BubbaTLC/author-clock/main/display_mgr.c

#include "display_mgr.h"

#include <stdio.h>
#include <string.h>
#include <stdlib.h>
#include "esp_log.h"
#include "esp_netif.h"
#include "nvs_config.h"

#include "EPD_7in5_V2.h"
#include "GUI_Paint.h"
#include "bmfont_renderer.h"
#include "fonts/font_select.h"
#include "weather_icons.h"

static const char *TAG = "DISPLAY_MGR";

// ─── Layout constants ────────────────────────────────────────────────────────
#define EPD_W 800
#define EPD_H 480

#define TIME_X 10
// Top bar height: must clear two font_ui lines (23+2+23=48px) plus padding → 70px
#define HRULE_Y 70
// Time text: one font_ui line (23px) vertically centred in [0, HRULE_Y]
#define TIME_Y ((HRULE_Y - 23) / 2) // = 23

// Weather block: right-aligned in the top bar, computed dynamically at render time
// Centre the 2-line text block (48px) in [0, HRULE_Y]; icon starts at same top edge
#define WEATHER_ICON_Y ((HRULE_Y - 48) / 2) // = 11
#define WEATHER_TEXT_GAP 6                  // pixels between icon right edge and text
#define WEATHER_MAX_X (EPD_W - 8)           // right boundary
#define WEATHER_MIN_LEFT 300                // keep clear of date/time on the left

// Quote area
#define QUOTE_X 20
#define QUOTE_MAX_WIDTH 760
#define ATTRIB_MAX_WIDTH (EPD_W - QUOTE_X - 8)

// ─── Image buffer ─────────────────────────────────────────────────────────────
#define IMAGE_SIZE (EPD_W * EPD_H / 8)
static uint8_t *s_image = NULL;
static bool s_initialized = false;

// ─── Helper: enhanced word-wrap with bmfont support ──────────────────────────
// Returns the Y position immediately after the last drawn line (useful for placing
// elements dynamically below the text block). Handles timeString portion in bold.
// ─── Helper: measure line width using the correct font per segment ─────────────
// Uses bold_font for characters that fall within [ts_pos, ts_pos+ts_len),
// regular font for everything else. Matches how the line will actually be drawn.
static uint16_t mixed_string_width(const char *p, int len, const bmfont_t *font,
                                   const bmfont_t *bold_font, const char *ts_pos, int ts_len) {
    char buf[512];
    int n;

    // Fast path: no bold overlap in this segment
    if (!bold_font || !ts_pos || ts_len == 0 || ts_pos >= p + len || ts_pos + ts_len <= p) {
        n = len < (int)sizeof(buf) - 1 ? len : (int)sizeof(buf) - 1;
        memcpy(buf, p, n);
        buf[n] = '\0';
        return bmfont_string_width(buf, font);
    }

    uint16_t w = 0;

    // Prefix in regular font: [p, ts_pos)
    if (ts_pos > p) {
        n = (int)(ts_pos - p);
        n = n < (int)sizeof(buf) - 1 ? n : (int)sizeof(buf) - 1;
        memcpy(buf, p, n);
        buf[n] = '\0';
        w += bmfont_string_width(buf, font);
    }

    // Bold section: intersect [ts_pos, ts_pos+ts_len) with [p, p+len)
    const char *bold_start = ts_pos > p ? ts_pos : p;
    const char *bold_end = (ts_pos + ts_len) < (p + len) ? (ts_pos + ts_len) : (p + len);
    if (bold_end > bold_start) {
        n = (int)(bold_end - bold_start);
        n = n < (int)sizeof(buf) - 1 ? n : (int)sizeof(buf) - 1;
        memcpy(buf, bold_start, n);
        buf[n] = '\0';
        w += bmfont_string_width(buf, bold_font);
    }

    // Suffix in regular font: [ts_pos+ts_len, p+len)
    if (ts_pos + ts_len < p + len) {
        const char *sfx = ts_pos + ts_len;
        n = (int)((p + len) - sfx);
        n = n < (int)sizeof(buf) - 1 ? n : (int)sizeof(buf) - 1;
        memcpy(buf, sfx, n);
        buf[n] = '\0';
        w += bmfont_string_width(buf, font);
    }

    return w;
}

static int text_wrap_bmfont(const char *text, const char *timestring, const bmfont_t *font,
                            const bmfont_t *bold_font, uint16_t x, uint16_t y, uint16_t max_width,
                            uint16_t max_y, bool dry_run) {
    if (!text || !font)
        return 0;

    uint16_t line_height = bmfont_height(font);
    uint16_t bold_line_height = bold_font ? bmfont_height(bold_font) : line_height;
    if (bold_line_height > line_height)
        line_height = bold_line_height;

    int lines = 0;
    uint16_t cur_y = y;

    char line_buf[128];
    const char *p = text;
    const char *timestring_pos = timestring ? strstr(text, timestring) : NULL;
    int ts_len = (timestring && timestring_pos) ? (int)strlen(timestring) : 0;

    while (*p && cur_y + line_height <= max_y) {
        // Find how many characters fit on this line (word-boundary break)
        int len = 0;
        int last_space = -1;
        uint16_t line_width = 0;

        // Calculate how much text fits, measuring bold sections with bold_font
        while (p[len]) {
            if (p[len] == ' ') {
                // Don't use spaces inside the timestring as break points — the
                // timestring must stay on a single line so it renders fully bold.
                bool in_ts = timestring_pos && ts_len > 0 && (p + len) >= timestring_pos &&
                             (p + len) < (timestring_pos + ts_len);
                if (!in_ts)
                    last_space = len;
            }
            if (p[len] == '\n') {
                last_space = len;
                break;
            }

            line_width = mixed_string_width(p, len + 1, font, bold_font, timestring_pos, ts_len);

            if (line_width >= max_width) {
                break;
            }

            len++;
        }

        // If the remaining text fits entirely, take it all
        if (p[len] == '\0') {
            // fall through with len as-is
        } else if (last_space > 0) {
            len = last_space; // break at last word boundary
        } else if (len == 0) {
            len = 1; // Force at least one character to avoid infinite loop
        }

        // Copy line
        int copy = len < (int)sizeof(line_buf) - 1 ? len : (int)sizeof(line_buf) - 1;
        memcpy(line_buf, p, copy);
        line_buf[copy] = '\0';

        if (!dry_run) {
            // Check if this line contains the timestring
            bool has_timestring =
                timestring_pos && (timestring_pos >= p) && (timestring_pos < p + len);

            if (has_timestring && bold_font && timestring) {
                int prefix_len = timestring_pos - p;
                int timestring_len = strlen(timestring);

                uint16_t cur_x = x;

                if (prefix_len > 0) {
                    char prefix[128];
                    int prefix_copy = prefix_len < 127 ? prefix_len : 127;
                    memcpy(prefix, p, prefix_copy);
                    prefix[prefix_copy] = '\0';
                    cur_x += bmfont_draw_string(cur_x, cur_y, prefix, font, BLACK, WHITE);
                }

                cur_x += bmfont_draw_string(cur_x, cur_y, timestring, bold_font, BLACK, WHITE);

                const char *suffix = timestring_pos + timestring_len;
                if (suffix < p + len) {
                    int suffix_len = (p + len) - suffix;
                    if (suffix_len > 0 && suffix_len < 128) {
                        char suffix_buf[128];
                        memcpy(suffix_buf, suffix, suffix_len);
                        suffix_buf[suffix_len] = '\0';
                        bmfont_draw_string(cur_x, cur_y, suffix_buf, font, BLACK, WHITE);
                    }
                }
            } else {
                bmfont_draw_string(x, cur_y, line_buf, font, BLACK, WHITE);
            }
        }

        // Advance past the line content and optional space/newline
        p += len;
        if (*p == ' ' || *p == '\n')
            p++;

        cur_y += line_height;
        lines++;
    }
    return cur_y;
}

// ─── Helper: clean text encoding issues ───────────────────────────────────────
static void clean_text_encoding(char *text) {
    if (!text)
        return;

    char *p = text;
    while (*p) {
        // Replace UTF-8 smart quotes with regular ASCII quotes
        if ((unsigned char)*p == 0xe2 && (unsigned char)*(p + 1) == 0x80) {
            if ((unsigned char)*(p + 2) == 0x98 || (unsigned char)*(p + 2) == 0x99) {
                // Left/right single quotes → regular apostrophe
                *p = '\'';
                memmove(p + 1, p + 3, strlen(p + 3) + 1);
            } else if ((unsigned char)*(p + 2) == 0x9c || (unsigned char)*(p + 2) == 0x9d) {
                // Left/right double quotes → regular quotes
                *p = '"';
                memmove(p + 1, p + 3, strlen(p + 3) + 1);
            } else if ((unsigned char)*(p + 2) == 0x94) {
                // Em dash → regular dash
                *p = '-';
                memmove(p + 1, p + 3, strlen(p + 3) + 1);
            } else {
                p++;
            }
        } else if ((unsigned char)*p >= 128) {
            // Replace any other non-ASCII characters with space
            *p = ' ';
            p++;
        } else {
            p++;
        }
    }
}

// ─── Helper: format combined date/time string ────────────────────────────────
static void format_datetime_string(char *buf, size_t len, uint8_t hour, uint8_t min,
                                   const char *date_str, bool use_24_hour) {
    if (!buf || !date_str)
        return;

    if (use_24_hour) {
        snprintf(buf, len, "%s, %02d:%02d", date_str, hour, min);
    } else {
        // Convert to 12-hour format
        const char *period = "AM";
        uint8_t display_hour = hour;

        if (hour == 0) {
            display_hour = 12; // midnight
        } else if (hour == 12) {
            period = "PM"; // noon
        } else if (hour > 12) {
            display_hour = hour - 12;
            period = "PM";
        }

        snprintf(buf, len, "%s, %d:%02d %s", date_str, display_hour, min, period);
    }
}

// ─── Helper: commit buffer to display ────────────────────────────────────────
// Always re-init before displaying: the display enters deep sleep after each
// EPD_7IN5_V2_Sleep() call and must be woken with a full init sequence before
// it will respond to commands or toggle the BUSY pin again.
static void flush_display(void) {
    EPD_7IN5_V2_Init();
    EPD_7IN5_V2_Display(s_image);
    EPD_7IN5_V2_Sleep();
}

// ─── Public API ──────────────────────────────────────────────────────────────

int display_mgr_init(void) {
    if (s_initialized)
        return 0;

    ESP_LOGI(TAG, "Initializing e-paper display");

    if (DEV_Module_Init() != 0) {
        ESP_LOGE(TAG, "DEV_Module_Init failed");
        return -1;
    }

    // Give the display hardware time to stabilize after power-on
    vTaskDelay(pdMS_TO_TICKS(2000));

    s_image = malloc(IMAGE_SIZE);
    if (!s_image) {
        ESP_LOGE(TAG, "Failed to allocate image buffer (%d bytes)", IMAGE_SIZE);
        return -2;
    }

    Paint_NewImage(s_image, EPD_W, EPD_H, ROTATE_0, WHITE);
    Paint_Clear(WHITE);

    // First initialization after cold boot - may need retry
    ESP_LOGI(TAG, "Performing initial EPD setup (may take extra time on cold boot)");
    for (int attempt = 0; attempt < 2; attempt++) {
        if (attempt > 0) {
            ESP_LOGW(TAG, "Retrying EPD initialization (attempt %d)", attempt + 1);
            vTaskDelay(pdMS_TO_TICKS(3000)); // Extra delay between attempts
        }

        EPD_7IN5_V2_Init();
        // Don't do initial clear on cold boot - it often fails and isn't necessary
        // since we'll be updating with content immediately anyway
        break;
    }

    s_initialized = true;
    ESP_LOGI(TAG, "Display initialized (800x480, %d byte buffer)", IMAGE_SIZE);
    return 0;
}

void display_mgr_show_provisioning(const char *ap_ssid, const char *ip_str) {
    if (!s_initialized)
        return;
    ESP_LOGI(TAG, "Showing provisioning screen");

    Paint_Clear(WHITE);

    bmfont_draw_string(10, 80, "Author Clock Setup", &font_ui, BLACK, WHITE);
    bmfont_draw_string(10, 130, "1. Connect your phone to WiFi:", &font_ui, BLACK, WHITE);

    char ssid_line[64];
    snprintf(ssid_line, sizeof(ssid_line), "   \"%s\"", ap_ssid ? ap_ssid : "AuthorClock");
    bmfont_draw_string(10, 155, ssid_line, &font_ui, BLACK, WHITE);

    bmfont_draw_string(10, 210, "2. Open a browser and visit:", &font_ui, BLACK, WHITE);

    char url_line[64];
    snprintf(url_line, sizeof(url_line), "   http://%s", ip_str ? ip_str : "192.168.4.69");
    bmfont_draw_string(10, 235, url_line, &font_ui, BLACK, WHITE);

    bmfont_draw_string(10, 295, "3. Fill in the form with your", &font_ui, BLACK, WHITE);
    bmfont_draw_string(10, 318, "   WiFi credentials and city.", &font_ui, BLACK, WHITE);

    flush_display();
}

void display_mgr_show_connecting(const char *ssid) {
    if (!s_initialized)
        return;
    ESP_LOGI(TAG, "Showing connecting screen for: %s", ssid ? ssid : "?");

    Paint_Clear(WHITE);
    bmfont_draw_string(10, 200, "Connecting to WiFi...", &font_ui, BLACK, WHITE);

    if (ssid) {
        char buf[64];
        snprintf(buf, sizeof(buf), "\"%s\"", ssid);
        bmfont_draw_string(10, 240, buf, &font_ui, BLACK, WHITE);
    }

    flush_display();
}

void display_mgr_show_error(const char *msg) {
    if (!s_initialized)
        return;
    ESP_LOGE(TAG, "Showing error: %s", msg ? msg : "(null)");

    Paint_Clear(WHITE);
    bmfont_draw_string(10, 190, "Error:", &font_ui, BLACK, WHITE);

    if (msg) {
        text_wrap_bmfont(msg, NULL, &font_ui, NULL, 10, 230, EPD_W - 20, EPD_H - 20, false);
    }

    flush_display();
}

void display_mgr_update(uint8_t time_h, uint8_t time_m, const char *date_str,
                        const quote_result_t *quote, const weather_data_t *weather) {
    if (!s_initialized)
        return;
    ESP_LOGI(TAG, "Updating display: %02d:%02d", time_h, time_m);

    Paint_Clear(WHITE);

    // ── Load display preferences ──────────────────────────────────────────────
    bool use_24_hour = true;
    date_display_mode_t date_mode = DATE_MODE_DATE_TIME;
    bool weather_enabled = true;
    temp_unit_t temp_unit = TEMP_UNIT_FAHRENHEIT;

    nvs_config_load_time_format(&use_24_hour);
    nvs_config_load_date_mode(&date_mode);
    nvs_config_load_weather_enabled(&weather_enabled);
    nvs_config_load_temp_unit(&temp_unit);

    // Suppress weather block if data isn't available yet
    bool show_weather = weather_enabled && weather && weather->valid;
    bool top_bar_visible = (date_mode != DATE_MODE_OFF) || show_weather;

    // ── Top bar ───────────────────────────────────────────────────────────────
    if (top_bar_visible) {
        // Date / time in top-left
        if (date_mode == DATE_MODE_DATE_ONLY) {
            bmfont_draw_string(TIME_X, TIME_Y, date_str ? date_str : "--", &font_ui, BLACK, WHITE);
        } else if (date_mode == DATE_MODE_DATE_TIME) {
            char datetime_str[80];
            format_datetime_string(datetime_str, sizeof(datetime_str), time_h, time_m, date_str,
                                   use_24_hour);
            bmfont_draw_string(TIME_X, TIME_Y, datetime_str, &font_ui, BLACK, WHITE);
        }

        // Weather in top-right
        if (show_weather) {
            // Build text strings first so we can measure them
            char temp_str[16];
            if (temp_unit == TEMP_UNIT_FAHRENHEIT) {
                int temp_f = (int)((weather->temp_c * 9.0f / 5.0f) + 32.0f + 0.5f);
                snprintf(temp_str, sizeof(temp_str),
                         "%d\xb0"
                         "F",
                         temp_f);
            } else {
                int temp_c = (int)(weather->temp_c + 0.5f);
                snprintf(temp_str, sizeof(temp_str),
                         "%d\xb0"
                         "C",
                         temp_c);
            }

            // Measure text widths to compute right-aligned block position
            uint16_t temp_w = bmfont_string_width(temp_str, &font_ui);
            uint16_t cond_w = bmfont_string_width(weather->condition, &font_ui);
            uint16_t text_block_w = temp_w > cond_w ? temp_w : cond_w;
            uint16_t total_w = ICON_SIZE + WEATHER_TEXT_GAP + text_block_w;
            uint16_t icon_x = (total_w < (WEATHER_MAX_X - WEATHER_MIN_LEFT))
                                  ? (WEATHER_MAX_X - total_w)
                                  : WEATHER_MIN_LEFT;
            uint16_t text_x = icon_x + ICON_SIZE + WEATHER_TEXT_GAP;

            // Draw icon
            weather_icon_draw(icon_x, WEATHER_ICON_Y, weather->icon, weather->weather_id);

            // Draw temp on first line of weather block
            bmfont_draw_string(text_x, WEATHER_ICON_Y, temp_str, &font_ui, BLACK, WHITE);

            // Draw condition on second line
            uint16_t text_line2_y = WEATHER_ICON_Y + bmfont_height(&font_ui) + 2;
            if (text_line2_y < HRULE_Y - 2) {
                bmfont_draw_string(text_x, text_line2_y, weather->condition, &font_ui, BLACK,
                                   WHITE);
            }
        }

        // Horizontal rule
        Paint_DrawLine(0, HRULE_Y, EPD_W, HRULE_Y, BLACK, DOT_PIXEL_1X1, LINE_STYLE_SOLID);
    }

    // ── Vertical centering for quote ──────────────────────────────────────────
    uint16_t quote_area_top = top_bar_visible ? (HRULE_Y + 10) : 0;
    uint16_t attrib_h = bmfont_height(&font_attrib);
    uint16_t body_h = bmfont_height(&font_body);

    // Determine early whether attribution fits on one line or needs two
    bool has_quote = (quote && quote->quote[0]);
    int attrib_lines = 1;
    char attrib_full[288];
    if (has_quote) {
        snprintf(attrib_full, sizeof(attrib_full), "%s - %s", quote->title, quote->author);
        if (bmfont_string_width(attrib_full, &font_attrib) > ATTRIB_MAX_WIDTH)
            attrib_lines = 2;
    }

    // Reserve bottom margin for attribution (lines × height + 30px gap + 10px padding)
    uint16_t attrib_total = (uint16_t)(attrib_lines * attrib_h) + 40;
    uint16_t available_h = EPD_H - quote_area_top - attrib_total;

    // Build the text for measurement
    char quoted_text[1026];
    char no_quote_msg[96];
    char time_str[16];
    const char *display_text = NULL;
    const char *display_ts = NULL;

    if (has_quote) {
        snprintf(quoted_text, sizeof(quoted_text), "\"%s\"", quote->quote);
        clean_text_encoding(quoted_text);
        display_text = quoted_text;
        display_ts = (quote->timestring[0]) ? quote->timestring : NULL;
    } else {
        if (use_24_hour) {
            snprintf(time_str, sizeof(time_str), "%02d:%02d", time_h, time_m);
        } else {
            uint8_t display_hour = time_h;
            const char *ampm = "AM";
            if (time_h == 0) {
                display_hour = 12;
            } else if (time_h == 12) {
                ampm = "PM";
            } else if (time_h > 12) {
                display_hour = time_h - 12;
                ampm = "PM";
            }
            snprintf(time_str, sizeof(time_str), "%d:%02d %s", display_hour, time_m, ampm);
        }
        snprintf(no_quote_msg, sizeof(no_quote_msg),
                 "Oh no looks like this time doesn't have a quote, but it is %s.", time_str);
        display_text = no_quote_msg;
        display_ts = time_str;
    }

    // Dry-run to measure quote block height
    // Use a large max_y so the full text is measured regardless of display limits
    int measured_end_y = text_wrap_bmfont(display_text, display_ts, &font_body, &font_body_bold,
                                          QUOTE_X, 0, QUOTE_MAX_WIDTH, EPD_H, true);
    uint16_t quote_block_h = (uint16_t)(measured_end_y > 0 ? measured_end_y : body_h);

    // Center the quote block in the available area (clamp to avoid overlap with top bar)
    uint16_t quote_y = quote_area_top;
    if (available_h > quote_block_h) {
        quote_y = quote_area_top + (available_h - quote_block_h) / 2;
    }

    // ── Quote ─────────────────────────────────────────────────────────────────
    uint16_t quote_max_y = EPD_H - attrib_total;
    int quote_end_y = text_wrap_bmfont(display_text, display_ts, &font_body, &font_body_bold,
                                       QUOTE_X, quote_y, QUOTE_MAX_WIDTH, quote_max_y, false);

    // ── Attribution ───────────────────────────────────────────────────────────
    if (has_quote) {
        int attrib_y = quote_end_y + 30;
        if (attrib_lines == 2) {
            // Two-line attribution: "{title} -" / "{author}"
            if (attrib_y > (int)(EPD_H - 2 * attrib_h - 4))
                attrib_y = EPD_H - 2 * attrib_h - 4;
            char title_line[288];
            snprintf(title_line, sizeof(title_line), "%s -", quote->title);
            bmfont_draw_string(QUOTE_X, (uint16_t)attrib_y, title_line, &font_attrib, BLACK, WHITE);
            bmfont_draw_string(QUOTE_X, (uint16_t)(attrib_y + attrib_h), quote->author,
                               &font_attrib, BLACK, WHITE);
        } else {
            if (attrib_y > (int)(EPD_H - attrib_h - 4))
                attrib_y = EPD_H - attrib_h - 4;
            bmfont_draw_string(QUOTE_X, (uint16_t)attrib_y, attrib_full, &font_attrib, BLACK,
                               WHITE);
        }
    }

    flush_display();
    ESP_LOGI(TAG, "Display update complete");
}
