BubbaTLC/author-clock/main/wifi_sta.c

#include "wifi_sta.h"
#include "app_config.h"

#include <string.h>
#include "freertos/FreeRTOS.h"
#include "freertos/task.h"
#include "freertos/event_groups.h"
#include "esp_wifi.h"
#include "esp_event.h"
#include "esp_log.h"
#include "esp_system.h"
#include "esp_netif.h"

static const char *TAG = "WIFI_STA";

// Event group bits
#define WIFI_CONNECTED_BIT BIT0
#define WIFI_FAIL_BIT BIT1

// Maximum number of connection retry attempts
#define MAX_RETRY 5

// Static variables
static EventGroupHandle_t s_wifi_event_group;
static int s_retry_num = 0;
static bool s_wifi_initialized = false;
static bool s_connected = false;

static void event_handler(void *arg, esp_event_base_t event_base, int32_t event_id,
                          void *event_data) {
    if (event_base == WIFI_EVENT && event_id == WIFI_EVENT_STA_START) {
        ESP_LOGI(TAG, "WiFi STA started, attempting connection...");
        esp_wifi_connect();
    } else if (event_base == WIFI_EVENT && event_id == WIFI_EVENT_STA_DISCONNECTED) {
        s_connected = false;
        if (s_retry_num < MAX_RETRY) {
            ESP_LOGI(TAG, "WiFi connection failed, retrying... (%d/%d)", s_retry_num + 1,
                     MAX_RETRY);
            esp_wifi_connect();
            s_retry_num++;
        } else {
            ESP_LOGE(TAG, "Failed to connect to WiFi after %d attempts", MAX_RETRY);
            xEventGroupSetBits(s_wifi_event_group, WIFI_FAIL_BIT);
        }
    } else if (event_base == IP_EVENT && event_id == IP_EVENT_STA_GOT_IP) {
        ip_event_got_ip_t *event = (ip_event_got_ip_t *)event_data;
        ESP_LOGI(TAG, "WiFi connected! IP: " IPSTR, IP2STR(&event->ip_info.ip));
        s_retry_num = 0;
        s_connected = true;
        xEventGroupSetBits(s_wifi_event_group, WIFI_CONNECTED_BIT);
    }
}

esp_err_t author_wifi_sta_connect(const char *ssid, const char *password) {
    if (ssid == NULL || password == NULL) {
        ESP_LOGE(TAG, "SSID or password is NULL");
        return ESP_ERR_INVALID_ARG;
    }

    // Reset connection state
    s_connected = false;
    s_retry_num = 0;

    // Initialize WiFi if not already done
    if (!s_wifi_initialized) {
        ESP_ERROR_CHECK(esp_netif_init());
        ESP_ERROR_CHECK(esp_event_loop_create_default());

        esp_netif_t *sta_netif = esp_netif_create_default_wifi_sta();
        if (sta_netif == NULL) {
            ESP_LOGE(TAG, "Failed to create default WiFi STA interface");
            return ESP_FAIL;
        }

        wifi_init_config_t cfg = WIFI_INIT_CONFIG_DEFAULT();
        ESP_ERROR_CHECK(esp_wifi_init(&cfg));

        s_wifi_initialized = true;
        ESP_LOGI(TAG, "WiFi STA initialized");
    }

    // Create event group
    s_wifi_event_group = xEventGroupCreate();
    if (s_wifi_event_group == NULL) {
        ESP_LOGE(TAG, "Failed to create event group");
        return ESP_FAIL;
    }

    // Register event handlers
    ESP_ERROR_CHECK(esp_event_handler_instance_register(WIFI_EVENT, ESP_EVENT_ANY_ID,
                                                        &event_handler, NULL, NULL));
    ESP_ERROR_CHECK(esp_event_handler_instance_register(IP_EVENT, IP_EVENT_STA_GOT_IP,
                                                        &event_handler, NULL, NULL));

    // Configure WiFi
    wifi_config_t wifi_config = {0};
    strlcpy((char *)wifi_config.sta.ssid, ssid, sizeof(wifi_config.sta.ssid));
    strlcpy((char *)wifi_config.sta.password, password, sizeof(wifi_config.sta.password));
    wifi_config.sta.threshold.authmode = WIFI_AUTH_WPA2_PSK;
    wifi_config.sta.pmf_cfg.capable = true;
    wifi_config.sta.pmf_cfg.required = false;

    ESP_LOGI(TAG, "Connecting to WiFi SSID: %s", ssid);

    ESP_ERROR_CHECK(esp_wifi_set_mode(WIFI_MODE_STA));
    ESP_ERROR_CHECK(esp_wifi_set_config(WIFI_IF_STA, &wifi_config));
    ESP_ERROR_CHECK(esp_wifi_start());

    // Wait for connection or failure
    EventBits_t bits = xEventGroupWaitBits(s_wifi_event_group, WIFI_CONNECTED_BIT | WIFI_FAIL_BIT,
                                           pdFALSE, pdFALSE, portMAX_DELAY);

    esp_err_t result = ESP_FAIL;

    if (bits & WIFI_CONNECTED_BIT) {
        ESP_LOGI(TAG, "Successfully connected to WiFi");
        result = ESP_OK;
    } else if (bits & WIFI_FAIL_BIT) {
        ESP_LOGE(TAG, "Failed to connect to WiFi");
        result = ESP_FAIL;
    } else {
        ESP_LOGE(TAG, "Unexpected event occurred");
        result = ESP_FAIL;
    }

    // Clean up event group
    vEventGroupDelete(s_wifi_event_group);
    s_wifi_event_group = NULL;

    return result;
}

esp_err_t author_wifi_sta_disconnect(void) {
    if (!s_wifi_initialized) {
        ESP_LOGW(TAG, "WiFi not initialized");
        return ESP_ERR_INVALID_STATE;
    }

    ESP_LOGI(TAG, "Disconnecting from WiFi...");
    s_connected = false;

    esp_err_t ret = esp_wifi_disconnect();
    if (ret != ESP_OK) {
        ESP_LOGE(TAG, "Failed to disconnect WiFi: %s", esp_err_to_name(ret));
        return ret;
    }

    ret = esp_wifi_stop();
    if (ret != ESP_OK) {
        ESP_LOGE(TAG, "Failed to stop WiFi: %s", esp_err_to_name(ret));
        return ret;
    }

    ESP_LOGI(TAG, "WiFi disconnected");
    return ESP_OK;
}

bool author_wifi_sta_is_connected(void) {
    return s_connected;
}
