BubbaTLC/author-clock/main/epd/GUI_Paint.c

#include "GUI_Paint.h"
#include <string.h>
#include <stdio.h>

#define DOT_PIXEL_DFT DOT_PIXEL_1X1
#define DOT_STYLE_DFT DOT_FILL_AROUND
#define FONT_BACKGROUND WHITE
#define IMAGE_BACKGROUND WHITE

PAINT Paint;

/******************************************************************************
function: Create Image
parameter:
    image   :   Pointer to the image cache
    width   :   The width of the picture
    Height  :   The height of the picture
    Rotate  :   Image rotation
    Color   :   Whether the picture is inverted
******************************************************************************/
void Paint_NewImage(UBYTE *image, UWORD Width, UWORD Height, UWORD Rotate, UWORD Color)
{
    Paint.Image = NULL;
    Paint.Image = image;

    Paint.WidthMemory = Width;
    Paint.HeightMemory = Height;
    Paint.Color = Color;    
    Paint.WidthByte = (Width % 8 == 0)? (Width / 8 ): (Width / 8 + 1);
    Paint.HeightByte = Height;    
    Paint.Rotate = Rotate;
    Paint.Mirror = MIRROR_NONE;
    
    if(Rotate == ROTATE_0 || Rotate == ROTATE_180) {
        Paint.Width = Width;
        Paint.Height = Height;
    } else {
        Paint.Width = Height;
        Paint.Height = Width;
    }
}

/******************************************************************************
function: Select Image
parameter:
    image : Pointer to the image cache
******************************************************************************/
void Paint_SelectImage(UBYTE *image)
{
    Paint.Image = image;
}

/******************************************************************************
function: Select Image Rotate
parameter:
    Rotate : 0,90,180,270
******************************************************************************/
void Paint_SetRotate(UWORD Rotate)
{
    Paint.Rotate = Rotate;
}

/******************************************************************************
function: Select Image mirror
parameter:
    mirror   :Not mirror,Horizontal mirror,Vertical mirror,Origin mirror
******************************************************************************/
void Paint_SetMirroring(UBYTE mirror)
{
    Paint.Mirror = mirror;
}

/******************************************************************************
function: Draw Pixels
parameter:
    Xpoint : At point X
    Ypoint : At point Y
    Color  : Painted colors
******************************************************************************/
void Paint_SetPixel(UWORD Xpoint, UWORD Ypoint, UWORD Color)
{
    if(Xpoint > Paint.Width || Ypoint > Paint.Height){
        return;
    }      
    UWORD X, Y;

    switch(Paint.Rotate) {
    case 0:
        X = Xpoint;
        Y = Ypoint;  
        break;
    case 90:
        X = Paint.WidthMemory - Ypoint - 1;
        Y = Xpoint;
        break;
    case 180:
        X = Paint.WidthMemory - Xpoint - 1;
        Y = Paint.HeightMemory - Ypoint - 1;
        break;
    case 270:
        X = Ypoint;
        Y = Paint.HeightMemory - Xpoint - 1;
        break;

    default:
        return;
    }
    
    switch(Paint.Mirror) {
    case MIRROR_NONE:
        break;
    case MIRROR_HORIZONTAL:
        X = Paint.WidthMemory - X - 1;
        break;
    case MIRROR_VERTICAL:
        Y = Paint.HeightMemory - Y - 1;
        break;
    case MIRROR_ORIGIN:
        X = Paint.WidthMemory - X - 1;
        Y = Paint.HeightMemory - Y - 1;
        break;
    default:
        break;
    }

    if(X > Paint.WidthMemory || Y > Paint.HeightMemory){
        return;
    }
    
    UDOUBLE Addr = X / 8 + Y * Paint.WidthByte;
    UBYTE Rdata = Paint.Image[Addr];
    if(Color == BLACK)
        Paint.Image[Addr] = Rdata & ~(0x80 >> (X % 8));
    else
        Paint.Image[Addr] = Rdata | (0x80 >> (X % 8));
}

/******************************************************************************
function: Clear the color of the picture
parameter:
    Color : Painted colors
******************************************************************************/
void Paint_Clear(UWORD Color)
{
    for (UWORD Y = 0; Y < Paint.HeightByte; Y++) {
        for (UWORD X = 0; X < Paint.WidthByte; X++ ) {//8 pixel =  1 byte
            UDOUBLE Addr = X + Y*Paint.WidthByte;
            Paint.Image[Addr] = Color;
        }
    }
}

/******************************************************************************
function: Clear the color of a window
parameter:
    Xstart : x starting point
    Ystart : Y starting point
    Xend   : x end point
    Yend   : y end point
    Color  : Painted colors
******************************************************************************/
void Paint_ClearWindows(UWORD Xstart, UWORD Ystart, UWORD Xend, UWORD Yend, UWORD Color)
{
    UWORD X, Y;
    for (Y = Ystart; Y < Yend; Y++) {
        for (X = Xstart; X < Xend; X++) {
            Paint_SetPixel(X, Y, Color);
        }
    }
}

/******************************************************************************
function: Draw Point(Xpoint, Ypoint) Fill the color
parameter:
    Xpoint		: The Xpoint coordinate of the point
    Ypoint		: The Ypoint coordinate of the point
    Color		: Painted color
    Dot_Pixel	: point size
    Dot_Style	: point Style
******************************************************************************/
void Paint_DrawPoint(UWORD Xpoint, UWORD Ypoint, UWORD Color, DOT_PIXEL Dot_Pixel, DOT_STYLE Dot_Style)
{
    if (Xpoint > Paint.Width || Ypoint > Paint.Height) {
        return;
    }

    int16_t XDir_Num , YDir_Num;
    if (Dot_Style == DOT_FILL_AROUND) {
        for (XDir_Num = 0; XDir_Num < 2 * Dot_Pixel - 1; XDir_Num++) {
            for (YDir_Num = 0; YDir_Num < 2 * Dot_Pixel - 1; YDir_Num++) {
                if((int)(Xpoint + XDir_Num - Dot_Pixel) < 0 || (int)(Ypoint + YDir_Num - Dot_Pixel) < 0)
                    break;
                Paint_SetPixel(Xpoint + XDir_Num - Dot_Pixel, Ypoint + YDir_Num - Dot_Pixel, Color);
            }
        }
    } else {
        for (XDir_Num = 0; XDir_Num <  Dot_Pixel; XDir_Num++) {
            for (YDir_Num = 0; YDir_Num <  Dot_Pixel; YDir_Num++) {
                Paint_SetPixel(Xpoint + XDir_Num - 1, Ypoint + YDir_Num - 1, Color);
            }
        }
    }
}

/******************************************************************************
function: Draw a line of arbitrary slope
parameter:
    Xstart ：Starting Xpoint point coordinates
    Ystart ：Starting Xpoint point coordinates
    Xend   ：End point Xpoint coordinate
    Yend   ：End point Ypoint coordinate
    Color  ：The color of the line segment
    Line_width : Line width
    Line_Style: Solid and dotted lines
******************************************************************************/
void Paint_DrawLine(UWORD Xstart, UWORD Ystart, UWORD Xend, UWORD Yend, UWORD Color, DOT_PIXEL Line_width, LINE_STYLE Line_Style)
{
    if (Xstart > Paint.Width || Ystart > Paint.Height ||
        Xend > Paint.Width || Yend > Paint.Height) {
        return;
    }

    UWORD Xpoint = Xstart;
    UWORD Ypoint = Ystart;
    int dx = (int)Xend - (int)Xstart >= 0 ? Xend - Xstart : Xstart - Xend;
    int dy = (int)Yend - (int)Ystart <= 0 ? Yend - Ystart : Ystart - Yend;

    // Increment direction, 1 is positive, -1 is counter;
    int XAddway = Xstart < Xend ? 1 : -1;
    int YAddway = Ystart < Yend ? 1 : -1;

    //Cumulative error
    int Esp = dx + dy;
    char Dotted_Len = 0;

    for (;;) {
        Dotted_Len++;
        //Painted dotted line, 2 point is really virtual
        if (Line_Style == LINE_STYLE_DOTTED && Dotted_Len % 3 == 0) {
            Paint_DrawPoint(Xpoint, Ypoint, IMAGE_BACKGROUND, Line_width, DOT_FILL_AROUND);
            Dotted_Len = 0;
        } else {
            Paint_DrawPoint(Xpoint, Ypoint, Color, Line_width, DOT_FILL_AROUND);
        }
        if (2 * Esp >= dy) {
            if (Xpoint == Xend)
                break;
            Esp += dy;
            Xpoint += XAddway;
        }
        if (2 * Esp <= dx) {
            if (Ypoint == Yend)
                break;
            Esp += dx;
            Ypoint += YAddway;
        }
    }
}

/******************************************************************************
function: Draw a rectangle
parameter:
    Xstart ：Rectangular  Starting Xpoint point coordinates
    Ystart ：Rectangular  Starting Xpoint point coordinates
    Xend   ：Rectangular  End point Xpoint coordinate
    Yend   ：Rectangular  End point Ypoint coordinate
    Color  ：The color of the Rectangular segment
    Line_width: Line width
    Draw_Fill : Whether to fill the inside of the rectangle
******************************************************************************/
void Paint_DrawRectangle(UWORD Xstart, UWORD Ystart, UWORD Xend, UWORD Yend, UWORD Color, DOT_PIXEL Line_width, DRAW_FILL Draw_Fill)
{
    if (Xstart > Paint.Width || Ystart > Paint.Height ||
        Xend > Paint.Width || Yend > Paint.Height) {
        return;
    }

    if (Draw_Fill) {
        UWORD Ypoint;
        for(Ypoint = Ystart; Ypoint < Yend; Ypoint++) {
            Paint_DrawLine(Xstart, Ypoint, Xend, Ypoint, Color , Line_width, LINE_STYLE_SOLID);
        }
    } else {
        Paint_DrawLine(Xstart, Ystart, Xend, Ystart, Color, Line_width, LINE_STYLE_SOLID);
        Paint_DrawLine(Xstart, Ystart, Xstart, Yend, Color, Line_width, LINE_STYLE_SOLID);
        Paint_DrawLine(Xend, Yend, Xend, Ystart, Color, Line_width, LINE_STYLE_SOLID);
        Paint_DrawLine(Xend, Yend, Xstart, Yend, Color, Line_width, LINE_STYLE_SOLID);
    }
}

/******************************************************************************
function: Use the 8-point method to draw a circle of the
            specified size at the specified position->
parameter:
    X_Center  ：Center X coordinate
    Y_Center  ：Center Y coordinate
    Radius    ：circle Radius
    Color     ：The color of the ：circle segment
    Line_width: Line width
    Draw_Fill : Whether to fill the inside of the Circle
******************************************************************************/
void Paint_DrawCircle(UWORD X_Center, UWORD Y_Center, UWORD Radius, UWORD Color, DOT_PIXEL Line_width, DRAW_FILL Draw_Fill)
{
    if (X_Center > Paint.Width || Y_Center >= Paint.Height) {
        return;
    }

    //Draw a circle from(0, R) as a starting point
    int16_t XCurrent, YCurrent;
    XCurrent = 0;
    YCurrent = Radius;

    //Cumulative error,judge the next point of the logo
    int16_t Esp = 3 - (Radius << 1 );

    int16_t sCountY;
    if (Draw_Fill == DRAW_FILL_FULL) {
        while (XCurrent <= YCurrent ) { //Realistic circles
            for (sCountY = XCurrent; sCountY <= YCurrent; sCountY ++ ) {
                Paint_DrawPoint(X_Center + XCurrent, Y_Center + sCountY, Color, DOT_PIXEL_DFT, DOT_STYLE_DFT);             //1
                Paint_DrawPoint(X_Center - XCurrent, Y_Center + sCountY, Color, DOT_PIXEL_DFT, DOT_STYLE_DFT);             //2
                Paint_DrawPoint(X_Center - sCountY, Y_Center + XCurrent, Color, DOT_PIXEL_DFT, DOT_STYLE_DFT);             //3
                Paint_DrawPoint(X_Center - sCountY, Y_Center - XCurrent, Color, DOT_PIXEL_DFT, DOT_STYLE_DFT);             //4
                Paint_DrawPoint(X_Center - XCurrent, Y_Center - sCountY, Color, DOT_PIXEL_DFT, DOT_STYLE_DFT);             //5
                Paint_DrawPoint(X_Center + XCurrent, Y_Center - sCountY, Color, DOT_PIXEL_DFT, DOT_STYLE_DFT);             //6
                Paint_DrawPoint(X_Center + sCountY, Y_Center - XCurrent, Color, DOT_PIXEL_DFT, DOT_STYLE_DFT);             //7
                Paint_DrawPoint(X_Center + sCountY, Y_Center + XCurrent, Color, DOT_PIXEL_DFT, DOT_STYLE_DFT);
            }
            if (Esp < 0 )
                Esp += 4 * XCurrent + 6;
            else {
                Esp += 10 + 4 * (XCurrent - YCurrent );
                YCurrent --;
            }
            XCurrent ++;
        }
    } else { //Draw a hollow circle
        while (XCurrent <= YCurrent ) {
            Paint_DrawPoint(X_Center + XCurrent, Y_Center + YCurrent, Color, Line_width, DOT_STYLE_DFT);             //1
            Paint_DrawPoint(X_Center - XCurrent, Y_Center + YCurrent, Color, Line_width, DOT_STYLE_DFT);             //2
            Paint_DrawPoint(X_Center - YCurrent, Y_Center + XCurrent, Color, Line_width, DOT_STYLE_DFT);             //3
            Paint_DrawPoint(X_Center - YCurrent, Y_Center - XCurrent, Color, Line_width, DOT_STYLE_DFT);             //4
            Paint_DrawPoint(X_Center - XCurrent, Y_Center - YCurrent, Color, Line_width, DOT_STYLE_DFT);             //5
            Paint_DrawPoint(X_Center + XCurrent, Y_Center - YCurrent, Color, Line_width, DOT_STYLE_DFT);             //6
            Paint_DrawPoint(X_Center + YCurrent, Y_Center - XCurrent, Color, Line_width, DOT_STYLE_DFT);             //7
            Paint_DrawPoint(X_Center + YCurrent, Y_Center + XCurrent, Color, Line_width, DOT_STYLE_DFT);             //0

            if (Esp < 0 )
                Esp += 4 * XCurrent + 6;
            else {
                Esp += 10 + 4 * (XCurrent - YCurrent );
                YCurrent --;
            }
            XCurrent ++;
        }
    }
}

/******************************************************************************
function: Show English characters
parameter:
    Xpoint           ：X coordinate
    Ypoint           ：Y coordinate
    Acsii_Char       ：To display the characters
    Font             ：A structure pointer that displays a character size
    Color_Foreground : Select the foreground color
    Color_Background : Select the background color
******************************************************************************/
void Paint_DrawChar(UWORD Xpoint, UWORD Ypoint, const char Acsii_Char, sFONT* Font, UWORD Color_Foreground, UWORD Color_Background)
{
    UWORD Page, Column;

    if (Xpoint > Paint.Width || Ypoint > Paint.Height) {
        return;
    }

    uint32_t Char_Offset = (Acsii_Char - ' ') * Font->Height * (Font->Width / 8 + (Font->Width % 8 ? 1 : 0));
    const unsigned char *ptr = &Font->table[Char_Offset];

    for (Page = 0; Page < Font->Height; Page ++ ) {
        for (Column = 0; Column < Font->Width; Column ++ ) {
            //To determine whether the font background color and screen background color is consistent
            if (FONT_BACKGROUND == Color_Background) { //this process is to speed up the scan
                if (*ptr & (0x80 >> (Column % 8)))
                    Paint_SetPixel(Xpoint + Column, Ypoint + Page, Color_Foreground);
                //if (*ptr & (0x80 >> (Column % 8)))
                //    Paint_SetPixel(Xpoint + Column, Ypoint + Page, Color_Foreground);
                //else
                //    Paint_SetPixel(Xpoint + Column, Ypoint + Page, Color_Background);
            } else {
                if (*ptr & (0x80 >> (Column % 8))) {
                    Paint_SetPixel(Xpoint + Column, Ypoint + Page, Color_Foreground);
                } else {
                    Paint_SetPixel(Xpoint + Column, Ypoint + Page, Color_Background);
                }
            }
            //One pixel is 8 bits
            if (Column % 8 == 7)
                ptr++;
        }// Write a line
        if (Font->Width % 8 != 0)
            ptr++;
    }// Write all
}

/******************************************************************************
function:	Display the string
parameter:
    Xstart  ：X coordinate
    Ystart  ：Y coordinate
    pString ：A pointer to the string to be displayed
    Font    ：A structure pointer that displays a character size
    Color_Foreground : Select the foreground color
    Color_Background : Select the background color
******************************************************************************/
void Paint_DrawString_EN(UWORD Xstart, UWORD Ystart, const char * pString, sFONT* Font, UWORD Color_Foreground, UWORD Color_Background)
{
    UWORD Xpoint = Xstart;
    UWORD Ypoint = Ystart;

    if (Xstart > Paint.Width || Ystart > Paint.Height) {
        return;
    }

    while (* pString != '\0') {
        //if X direction filled , reposition to(Xstart,Ypoint),Ypoint is Y direction plus the Height of the character
        if ((Xpoint + Font->Width ) > Paint.Width ) {
            Xpoint = Xstart;
            Ypoint += Font->Height;
        }

        // If the Y direction is full, reposition to(Xstart, Ystart)
        if ((Ypoint  + Font->Height ) > Paint.Height ) {
            Xpoint = Xstart;
            Ypoint = Ystart;
        }
        Paint_DrawChar(Xpoint, Ypoint, * pString, Font, Color_Foreground, Color_Background);

        //The next character of the address
        pString ++;

        //The next word of the abscissa increases the font of the broadband
        Xpoint += Font->Width;
    }
}

/******************************************************************************
function: Display nummber
parameter:
    Xstart  ：X coordinate
    Ystart  : Y coordinate
    Nummber : The number displayed
    Font    ：A structure pointer that displays a character size
    Color_Foreground : Select the foreground color
    Color_Background : Select the background color
******************************************************************************/
#define  ARRAY_LEN 255
void Paint_DrawNum(UWORD Xpoint, UWORD Ypoint, int32_t Nummber, sFONT* Font, UWORD Color_Foreground, UWORD Color_Background)
{

    int16_t Num_Bit = 0, Str_Bit = 0;
    uint8_t Str_Array[ARRAY_LEN] = {0}, Num_Array[ARRAY_LEN] = {0};
    uint8_t *pStr = Str_Array;

    if (Xpoint > Paint.Width || Ypoint > Paint.Height) {
        return;
    }

    //Converts a number to a string
    while (Nummber) {
        Num_Array[Num_Bit] = Nummber % 10 + '0';
        Num_Bit++;
        Nummber /= 10;
    }

    //The string is inverted
    while (Num_Bit > 0) {
        Str_Array[Str_Bit] = Num_Array[Num_Bit - 1];
        Str_Bit ++;
        Num_Bit --;
    }

    //show
    Paint_DrawString_EN(Xpoint, Ypoint, (const char*)pStr, Font, Color_Foreground, Color_Background);
}

/******************************************************************************
function: Display time
parameter:
    Xstart  ：X coordinate
    Ystart  : Y coordinate
    pTime   : Time-related structures
    Font    ：A structure pointer that displays a character size
    Color_Foreground : Select the foreground color
    Color_Background : Select the background color
******************************************************************************/
void Paint_DrawTime(UWORD Xstart, UWORD Ystart, PAINT_TIME *pTime, sFONT* Font, UWORD Color_Foreground, UWORD Color_Background)
{
    uint8_t value[12];  // Increased buffer size

    //Write data into the cache
    sprintf((char*)value, "%02d:%02d:%02d", pTime->Hour, pTime->Min, pTime->Sec);
    Paint_DrawString_EN(Xstart, Ystart, (const char*)value, Font, Color_Foreground, Color_Background);
}
